dev-000/Ioniser/Negative Ioniser/Negative_Ioniser_PCB_Layout.png

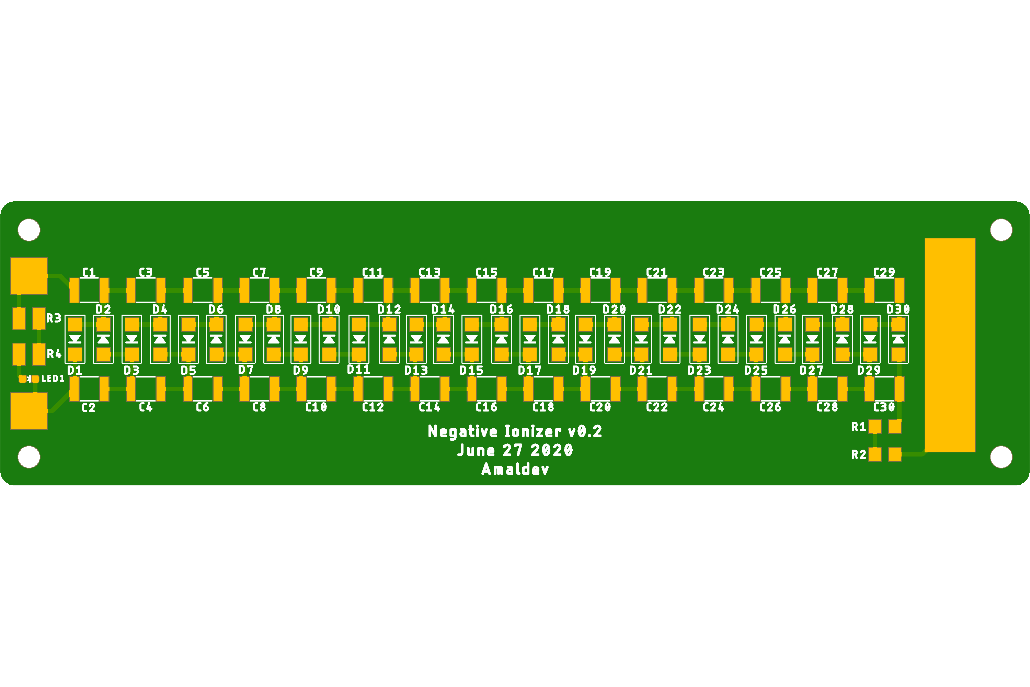
Negative Ioniser/Negative_Ioniser_PCB_Layout.png
