dev-000/Ioniser/LTSpice Simulation/Ioniser_LTspice.asc

C1: cap; 0.1µ; V=630 Irms=556m Rser=0.01433 Lser=0 mfg="KEMET" pn="C1812C104KBRAC" type="X7R"
C2: cap; 0.1µ; V=630 Irms=556m Rser=0.01433 Lser=0 mfg="KEMET" pn="C1812C104KBRAC" type="X7R"
C3: cap; 0.1µ; V=630 Irms=556m Rser=0.01433 Lser=0 mfg="KEMET" pn="C1812C104KBRAC" type="X7R"
C4: cap; 0.1µ; V=630 Irms=556m Rser=0.01433 Lser=0 mfg="KEMET" pn="C1812C104KBRAC" type="X7R"
C5: cap; 0.1µ; V=630 Irms=556m Rser=0.01433 Lser=0 mfg="KEMET" pn="C1812C104KBRAC" type="X7R"
C6: cap; 0.1µ; V=630 Irms=556m Rser=0.01433 Lser=0 mfg="KEMET" pn="C1812C104KBRAC" type="X7R"
C7: cap; 0.1µ; V=630 Irms=556m Rser=0.01433 Lser=0 mfg="KEMET" pn="C1812C104KBRAC" type="X7R"
C8: cap; 0.1µ; V=630 Irms=556m Rser=0.01433 Lser=0 mfg="KEMET" pn="C1812C104KBRAC" type="X7R"
C9: cap; 0.1µ; V=630 Irms=556m Rser=0.01433 Lser=0 mfg="KEMET" pn="C1812C104KBRAC" type="X7R"
C10: cap; 0.1µ; V=630 Irms=556m Rser=0.01433 Lser=0 mfg="KEMET" pn="C1812C104KBRAC" type="X7R"
C11: cap; 0.1µ; V=630 Irms=556m Rser=0.01433 Lser=0 mfg="KEMET" pn="C1812C104KBRAC" type="X7R"
C12: cap; 0.1µ; V=630 Irms=556m Rser=0.01433 Lser=0 mfg="KEMET" pn="C1812C104KBRAC" type="X7R"
C13: cap; 0.1µ; V=630 Irms=556m Rser=0.01433 Lser=0 mfg="KEMET" pn="C1812C104KBRAC" type="X7R"
C14: cap; 0.1µ; V=630 Irms=556m Rser=0.01433 Lser=0 mfg="KEMET" pn="C1812C104KBRAC" type="X7R"
C15: cap; 0.1µ; V=630 Irms=556m Rser=0.01433 Lser=0 mfg="KEMET" pn="C1812C104KBRAC" type="X7R"
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
R3: res; 10000k
R4: res; 10000k
R5: res; 10000k
R6: res; 10000k
V1: voltage; SINE(0 230 50)
V2: voltage; SINE(0 230 50)
V3: voltage; SINE(0 230 50)
Named nets: 0, Positive_Output, Negative_Output, Input_AC, Postive_AC_Output
.tran 50
Postive Ioniser
Negative Ioniser
Postive Ioniser AC Output
