dev-000/Ioniser/LTSpice Simulation/Simulation Results.png

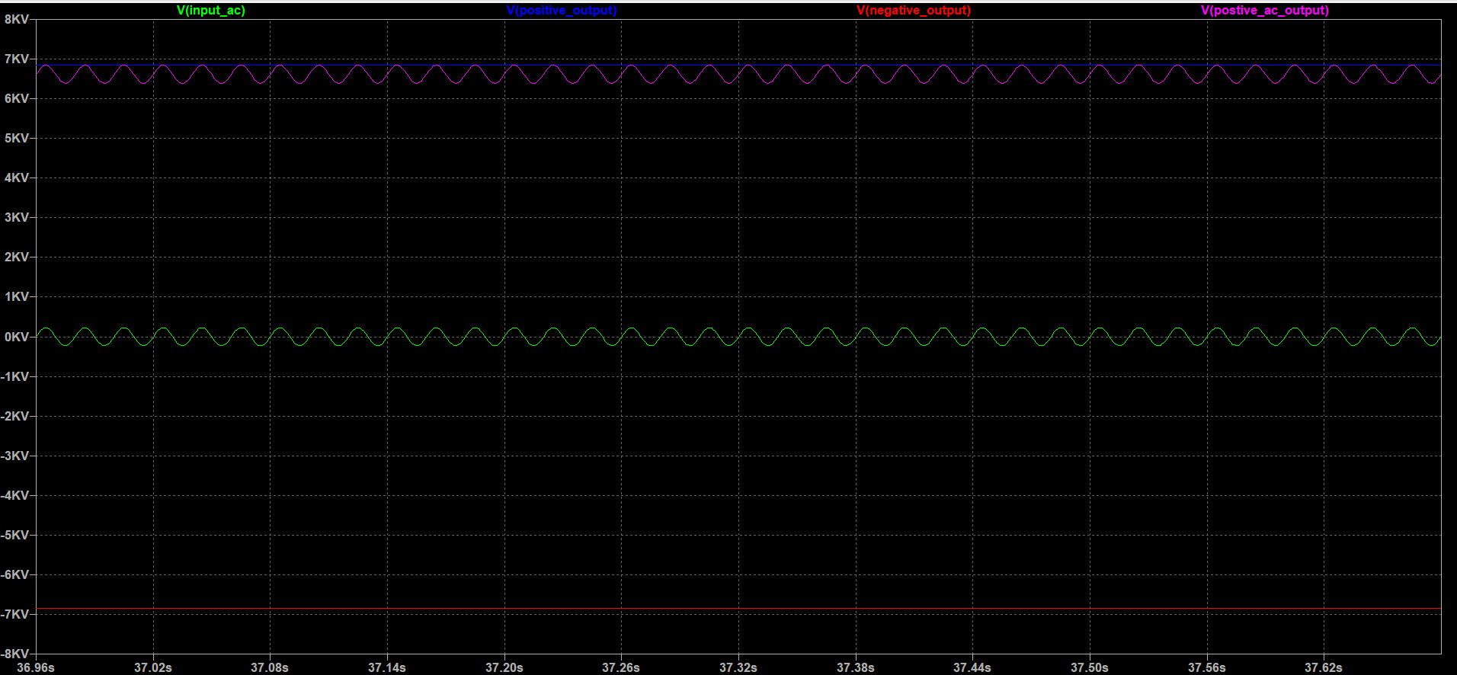
LTSpice Simulation/Simulation Results.png
